fpoussin/MotoLink/GUI/res/images/explosion-hi.png

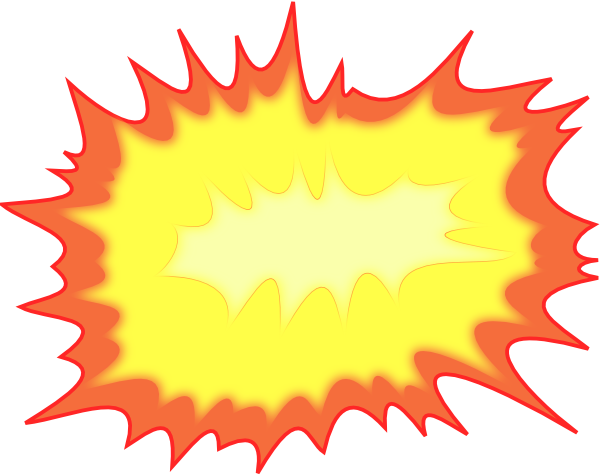
GUI/res/images/explosion-hi.png
