fpoussin/MotoLink/code/common/mcuconf_community.h

/*
    ChibiOS/RT - Copyright (C) 2014 Uladzimir Pylinsky aka barthess

    Licensed under the Apache License, Version 2.0 (the "License");
    you may not use this file except in compliance with the License.
    You may obtain a copy of the License at

        http://www.apache.org/licenses/LICENSE-2.0

    Unless required by applicable law or agreed to in writing, software
    distributed under the License is distributed on an "AS IS" BASIS,
    WITHOUT WARRANTIES OR CONDITIONS OF ANY KIND, either express or implied.
    See the License for the specific language governing permissions and
    limitations under the License.
*/

/*
 * FSMC driver system settings.
 */
#define STM32_FSMC_USE_FSMC1 FALSE
#define STM32_FSMC_FSMC1_IRQ_PRIORITY 10

/*
 * FSMC NAND driver system settings.
 */
#define STM32_NAND_USE_FSMC_NAND1 FALSE
#define STM32_NAND_USE_FSMC_NAND2 FALSE
#define STM32_NAND_USE_EXT_INT FALSE
#define STM32_NAND_DMA_STREAM STM32_DMA_STREAM_ID(2, 7)
#define STM32_NAND_DMA_PRIORITY 0
#define STM32_NAND_DMA_ERROR_HOOK(nandp) osalSysHalt("DMA failure")

/*
 * FSMC SRAM driver system settings.
 */
#define STM32_USE_FSMC_SRAM FALSE
#define STM32_SRAM_USE_FSMC_SRAM1 FALSE
#define STM32_SRAM_USE_FSMC_SRAM2 FALSE
#define STM32_SRAM_USE_FSMC_SRAM3 FLASE
#define STM32_SRAM_USE_FSMC_SRAM4 FALSE

/*
 * FSMC PC card driver system settings.
 */
#define STM32_USE_FSMC_PCARD FALSE

/*
 * FSMC SDRAM driver system settings.
 */
#define STM32_USE_FSMC_SDRAM FALSE

/*
 * EICU driver system settings.
 */
#define STM32_EICU_USE_TIM1 FALSE
#define STM32_EICU_USE_TIM2 FALSE
#define STM32_EICU_USE_TIM3 TRUE
#define STM32_EICU_USE_TIM4 FALSE
#define STM32_EICU_USE_TIM5 FALSE
#define STM32_EICU_USE_TIM8 FALSE
#define STM32_EICU_USE_TIM9 FALSE
#define STM32_EICU_USE_TIM10 FALSE
#define STM32_EICU_USE_TIM11 FALSE
#define STM32_EICU_USE_TIM12 FALSE
#define STM32_EICU_USE_TIM13 FALSE
#define STM32_EICU_USE_TIM14 FALSE
#define STM32_EICU_TIM1_IRQ_PRIORITY 7
#define STM32_EICU_TIM2_IRQ_PRIORITY 7
#define STM32_EICU_TIM3_IRQ_PRIORITY 7
#define STM32_EICU_TIM4_IRQ_PRIORITY 7
#define STM32_EICU_TIM5_IRQ_PRIORITY 7
#define STM32_EICU_TIM8_IRQ_PRIORITY 7
#define STM32_EICU_TIM9_IRQ_PRIORITY 7
#define STM32_EICU_TIM10_IRQ_PRIORITY 7
#define STM32_EICU_TIM11_IRQ_PRIORITY 7
#define STM32_EICU_TIM12_IRQ_PRIORITY 7
#define STM32_EICU_TIM13_IRQ_PRIORITY 7
#define STM32_EICU_TIM14_IRQ_PRIORITY 7

/*
 * TIMCAP driver system settings.
 */
#define STM32_TIMCAP_USE_TIM1 FALSE
#define STM32_TIMCAP_USE_TIM2 FALSE
#define STM32_TIMCAP_USE_TIM3 TRUE
#define STM32_TIMCAP_USE_TIM4 FALSE
#define STM32_TIMCAP_USE_TIM5 FALSE
#define STM32_TIMCAP_USE_TIM8 FALSE
#define STM32_TIMCAP_USE_TIM9 FALSE
#define STM32_TIMCAP_TIM1_IRQ_PRIORITY 3
#define STM32_TIMCAP_TIM2_IRQ_PRIORITY 3
#define STM32_TIMCAP_TIM3_IRQ_PRIORITY 3
#define STM32_TIMCAP_TIM4_IRQ_PRIORITY 3
#define STM32_TIMCAP_TIM5_IRQ_PRIORITY 3
#define STM32_TIMCAP_TIM8_IRQ_PRIORITY 3
#define STM32_TIMCAP_TIM9_IRQ_PRIORITY 3

/*
 * CRC driver system settings.
 */
#define STM32_CRC_USE_CRC1 TRUE
#define STM32_CRC_CRC1_DMA_IRQ_PRIORITY 5
#define STM32_CRC_CRC1_DMA_PRIORITY 2
#define STM32_CRC_CRC1_DMA_STREAM STM32_DMA_STREAM_ID(2, 1)

#define CRCSW_USE_CRC1 FALSE
#define CRCSW_CRC32_TABLE TRUE
#define CRCSW_CRC16_TABLE TRUE
#define CRCSW_PROGRAMMABLE TRUE
