fpoussin/MotoLink/code/app/tables.c

/*
 * tables.c
 *
 *  Created on: 20 nov. 2014
 *      Author: Mobyfab
 */

#include "tables.h"

/* Columns are divided by 100 */
cell_cols_t tableColumns = {0,   20,  40,  55,  70,  80,  90,  100,
                            110, 120, 130, 140, 150, 160, 165, 180};
cell_rows_t tableRows = {0, 2, 5, 7, 12, 25, 35, 50, 70, 85, 100};

cell_table_t tableAFR;
cell_table_t tableKnock;

void writeRows(uint8_t *rows, uint8_t size) {
  uint8_t i;
  for (i = 0; i < size; i++) {
    tableRows[i] = rows[i];
  }
}

void writeColumns(uint8_t *columns, uint8_t size) {
  uint8_t i;
  for (i = 0; i < size; i++) {
    tableColumns[i] = columns[i];
  }
}

CCM_FUNC bool findCell(uint8_t tp, uint16_t rpm, uint8_t *row, uint8_t *col) {
  uint8_t i, maxcol, maxrow;
  bool rowFound = false, colFound = false;

  *row = 0;
  *col = 0;
  rpm /= 100;

  maxrow = sizeof(tableRows) - 1;
  maxcol = sizeof(tableColumns) - 1;

  if (tp >= tableRows[maxrow]) {
    *row = maxrow;
    rowFound = true;
  } else if (tp <= tableRows[0]) {
    *row = 0;
    rowFound = true;
  } else {
    for (i = 0; i < maxrow; i++) {
      uint8_t h = tableRows[i];
      uint8_t h2 = tableRows[i + 1];

      if (tp >= h && tp <= h2) {
        *row = i;
        rowFound = true;
        break;
      }
    }
  }

  if (rpm >= tableColumns[maxcol]) {
    *col = maxcol;
    colFound = true;
  } else if (rpm <= tableColumns[0]) {
    *col = 0;
    colFound = true;
  } else {
    for (i = 0; i < maxcol; i++) {
      uint8_t h = tableColumns[i];
      uint8_t h2 = tableColumns[i + 1];

      if (rpm >= h && rpm <= h2) {
        *col = i;
        colFound = true;
        break;
      }
    }
  }

  return rowFound && colFound;
}
