fpoussin/MotoLink/GUI/src/mainwindow.cpp

#include "mainwindow.h"
#include <QShortcut>
#include <QSignalMapper>
#include <ui_main.h>
#include <ui_tasks.h>
#include <ui_knock.h>
#include <ui_logs.h>
#include <QFileInfo>
#include <QModelIndex>
#include <QDateTime>
#include <QItemSelection>

MainWindow::MainWindow(QWidget *parent)
    : QMainWindow(parent), mSettings("Motolink", "Motolink"), mHelpViewer(NULL), mUndoStack(NULL), mAFRModel(&mUndoStack, 7.0, 24.0, 13.0, false, false), mAFRTgtModel(&mUndoStack, 8.0, 24.0, 13.0), mKnockModel(&mUndoStack, 0, 512, 0, false, false), mFuelOffsetModel(&mUndoStack, -30, 30, 0, false, false)
{
    mMainUi = new Ui::MainWindow();
    mTasksUi = new Ui::Tasks();
    mLogsUi = new Ui::Logs();
    mSerialLogsUi = new Ui::Logs();
    mKnockGraphUi = new Ui::KnockGraph();

    mTasksWidget = new QWidget();
    mKnockGraphWidget = new QWidget;
    mLogsWidget = new QWidget();
    mSerialLogsWidget = new QWidget();

    mMainUi->setupUi(this);
    mTasksUi->setupUi(mTasksWidget);
    mKnockGraphUi->setupUi(mKnockGraphWidget);
    mLogsUi->setupUi(mLogsWidget);
    mSerialLogsUi->setupUi(mSerialLogsWidget);

    mMtl = new Motolink();
    mUpdateWizard = new UpdateWizard(mMtl);

    mUndoStack.setUndoLimit(100);

    this->setupDefaults();
    this->setupConnections();
    this->setupTabShortcuts();
    this->setupSettings();
    this->setupKnockGraph();

    mUndoView.setStack(&mUndoStack);
    mUndoView.setWindowTitle(tr("Actions History - ") + this->windowTitle());
    mHasChanged = false;

    mFastPollingTimer.setInterval(25);
    mSlowPollingTimer.setInterval(500);
    mTablesTimer.setInterval(25);
    mRedrawTimer.setInterval(25);

    this->exportToMTLFile();
    this->uiDisable();
    mHeadersUpdating = false;

    emit signalStartupComplete();

    this->log(tr("Ready"));
}

MainWindow::~MainWindow()
{
    delete mMainUi;
    delete mUpdateWizard;
    delete mTasksUi;
    delete mTasksWidget;
    delete mKnockGraphUi;
    delete mKnockGraphWidget;
    delete mLogsUi;
    delete mSerialLogsUi;
    delete mLogsWidget;
    delete mMtl;

    for (int i = 0; i < MAX_RECENT_FILES; ++i) {
        if (mRecentFilesActions[i] != NULL)
            delete mRecentFilesActions[i];
    }
}

void MainWindow::Quit()
{
    if (mHasChanged) {

        int ret = QMessageBox::question(this, tr("Confirm"),
                                        tr("Unsaved changes!\nSave file before closing?"),
                                        QMessageBox::Save | QMessageBox::Discard
                                                | QMessageBox::Cancel,
                                        QMessageBox::Cancel);

        switch (ret) {
        case QMessageBox::Save:
            this->saveFile();
            break;
        case QMessageBox::Discard:
            break;
        case QMessageBox::Cancel:
            return;
        }
    }
    qApp->quit();
}

void MainWindow::closeEvent(QCloseEvent *event)
{
    event->ignore();
    this->Quit();
}

void MainWindow::openFile(void)
{
    QString fileName(QFileDialog::getOpenFileName(this,
                                                  tr("Open Tune File"), "", tr("Tune Files (*.xml)")));

    this->openFile(fileName);
}

void MainWindow::openFile(const QString &filename)
{
    if (filename.isEmpty())
        return;

    QStringList files = mSettings.value(SETTINGS_RECENT_FILES).toStringList();

    mCurrentFile = filename;
    files.removeAll(filename);
    files.prepend(filename);
    while (files.size() > MAX_RECENT_FILES)
        files.removeLast();

    mSettings.setValue(SETTINGS_RECENT_FILES, files);
    this->updateRecentFilesActions();

    QFile file(mCurrentFile);

    if (!file.open(QFile::ReadOnly)) {
        this->log(tr("Failed to open file for reading!"));
        return;
    }

    mFile.read(&file);
    file.close();

    this->log(tr("Opened ") + filename);

    this->importFromMTLFile();
}

void MainWindow::saveFile(void)
{
    if (mCurrentFile.length() == 0) {
        this->saveFileAs();
        return;
    }

    QFile file(mCurrentFile);

    qWarning() << "Saving" << mCurrentFile;
    if (!file.open(QFile::WriteOnly)) {
        qWarning() << tr("Failed to open file for writing!") << mCurrentFile;
        this->log(tr("Failed to open file for writing!"));
        return;
    }

    file.seek(0);
    this->exportToMTLFile();
    mFile.write(&file);
    file.close();
    this->log(tr("File saved."));

    mHasChanged = false;
}

void MainWindow::saveFileAs(void)
{
    QString fileName(QFileDialog::getSaveFileName(this,
                                                  tr("Save Tune File"), "", tr("Tune Files (*.xml)")));

    if (fileName.isEmpty()) {
        return;
    }
    mCurrentFile = fileName;

    this->saveFile();
}

void MainWindow::connectMtl()
{
    if (mMtl->usbConnect()) {
        mMtl->bootAppIfNeeded();
        mMtl->readTablesHeaders();
        this->uiEnable();
        mFastPollingTimer.start();
        mSlowPollingTimer.start();
        mTablesTimer.start();
        mRedrawTimer.start();
        onReadMtlSettings();
        this->log(tr("Connected"));
    } else {
        this->log(tr("Connection Failed"));
    }
}

void MainWindow::disconnectMtl()
{
    mFastPollingTimer.stop();
    mSlowPollingTimer.stop();
    mTablesTimer.stop();
    mRedrawTimer.stop();
    mMtl->usbDisconnect();
    this->uiDisable();
    this->log(tr("Disconnected"));
}

void MainWindow::showAbout()
{
    QString Fwv = mUpdateWizard->getFwVersion();
    QMessageBox::information(this, tr("About Motolink"),
                             tr("<strong>App Version: ") + __MTL_VER__ + "</strong><br/>" + tr("<strong>Bundled firmware Version: ") + Fwv + "</strong><br/>" + tr("Built on: ") + QString(__DATE__) + " " + QString(__TIME__) + "<br/><br/>" + tr("Motolink is a smart ECU mapping interface.<br/><br/>"
                                                                                                                                                                                                                                                   "You can find more information "
                                                                                                                                                                                                                                                   "<a href=\"https://github.com/fpoussin/MotoLink\">here.</a>"));
}

void MainWindow::showUpdateDialog()
{
    mUpdateWizard->showWizard();
}

void MainWindow::setupDefaults(void)
{
    this->setWindowTitle(QString("Motolink ") + __MTL_VER__);

    mTablesModelList.append(&mAFRModel);
    mTablesModelList.append(&mAFRTgtModel);
    mTablesModelList.append(&mKnockModel);
    mTablesModelList.append(&mFuelOffsetModel);

    mTablesViewList.append(mMainUi->tableAfrMap);
    mTablesViewList.append(mMainUi->tableAfrTgt);
    mTablesViewList.append(mMainUi->tableKnk);
    mTablesViewList.append(mMainUi->tableFuelOffset);

    mAFRModel.setName(tr("AFR"));
    mAFRTgtModel.setName(tr("AFR Target"));
    mKnockModel.setName(tr("Knock"));

    mAFRModel.setId(1);
    mKnockModel.setId(2);

    mDegreeSuffix.setSuffix(QString::fromUtf8("°"));
    mPercentSuffix.setSuffix("%");

    mMainUi->tableAfrMap->setItemDelegate(&mAfrDisplay);
    mMainUi->tableAfrTgt->setItemDelegate(&mAfrDisplay);
    mMainUi->tableFuelOffset->setItemDelegate(&mPercentSuffix);

    mMainUi->tableAfrMap->setModel(&mAFRModel);
    mMainUi->tableAfrTgt->setModel(&mAFRTgtModel);
    mMainUi->tableKnk->setModel(&mKnockModel);
    mMainUi->tableFuelOffset->setModel(&mFuelOffsetModel);

    mMainUi->tableAfrMap->setMenuReadOnly(true);
    mMainUi->tableKnk->setMenuReadOnly(true);
    mMainUi->tableFuelOffset->setMenuReadOnly(true);
}

void MainWindow::setupConnections(void)
{
    QObject::connect(mMainUi->actionAbout, SIGNAL(triggered()), this, SLOT(showAbout()));
    QObject::connect(mMainUi->actionAbout_QT, SIGNAL(triggered()), qApp, SLOT(aboutQt()));
    QObject::connect(mMainUi->actionQuit, SIGNAL(triggered()), this, SLOT(Quit()));
    QObject::connect(mMainUi->actionOpen, SIGNAL(triggered()), this, SLOT(openFile()));
    QObject::connect(mMainUi->actionSave, SIGNAL(triggered()), this, SLOT(saveFile()));
    QObject::connect(mMainUi->actionSave_As, SIGNAL(triggered()), this, SLOT(saveFileAs()));
    QObject::connect(mMainUi->actionConnect, SIGNAL(triggered()), this, SLOT(connectMtl()));
    QObject::connect(mMainUi->actionDisconnect, SIGNAL(triggered()), this, SLOT(disconnectMtl()));
    QObject::connect(mMainUi->actionUpdate, SIGNAL(triggered()), this, SLOT(showUpdateDialog()));
    QObject::connect(mMainUi->actionEnglish, SIGNAL(triggered()), this, SLOT(setLanguageEnglish()));
    QObject::connect(mMainUi->actionFran_ais, SIGNAL(triggered()), this, SLOT(setLanguageFrench()));
    QObject::connect(mMainUi->actionShowHelpIndex, SIGNAL(triggered()), this, SLOT(showHelp()));
    QObject::connect(mMainUi->actionShow_tasks, SIGNAL(triggered()), this, SLOT(showTasks()));
    QObject::connect(mMainUi->actionShow_Knock_Spectrum, SIGNAL(triggered()), this, SLOT(showKnockGraph()));
    QObject::connect(mMainUi->actionShow_Logs, SIGNAL(triggered()), this, SLOT(showLogs()));
    QObject::connect(mMainUi->actionShow_Serial_Data, SIGNAL(triggered()), this, SLOT(showSerialData()));

    QObject::connect(mMainUi->actionShow_actions, SIGNAL(triggered()), &mUndoView, SLOT(show()));
    QObject::connect(mMainUi->actionUndo, SIGNAL(triggered()), &mUndoStack, SLOT(undo()));
    QObject::connect(mMainUi->actionRedo, SIGNAL(triggered()), &mUndoStack, SLOT(redo()));
    QObject::connect(&mUndoStack, SIGNAL(canRedoChanged(bool)), mMainUi->actionRedo, SLOT(setEnabled(bool)));
    QObject::connect(&mUndoStack, SIGNAL(canUndoChanged(bool)), mMainUi->actionUndo, SLOT(setEnabled(bool)));

    // Tables (color and cursor update)
    QObject::connect(&mAFRTgtModel, SIGNAL(cellValueChanged(int, int)), this, SLOT(onDataChanged()));
    QObject::connect(&mAFRTgtModel, SIGNAL(cellValueChanged(int, int)), this, SLOT(calculateFuelOffset(int, int)));
    QObject::connect(&mAFRModel, SIGNAL(cellValueChanged(int, int)), this, SLOT(calculateFuelOffset(int, int)));
    for (int i = 0; i < mTablesModelList.size(); i++) {
        TableModel *tbl = mTablesModelList.at(i);
        QObject::connect(tbl, SIGNAL(headerDataNeedSync(int, Qt::Orientation, QVariant)),
                         this, SLOT(onHeadersNeedSync(int, Qt::Orientation, QVariant)));
        //QObject::connect(tbl->view(), SIGNAL(modelUpdated(QWidget*)), mMainUi->tabMain, SLOT(setCurrentWidget(QWidget*)));
        if (tbl->id() > 1)
            QObject::connect(tbl->view(), SIGNAL(cellCleared(uint, int, int)), mMtl, SLOT(clearCell(uint, int, int)));
    }

    for (int i = 0; i < mSpinBoxList.size(); i++) {
        QSpinBox *sb = mSpinBoxList.at(i);
        QObject::connect(sb, SIGNAL(valueChanged(int)), this, SLOT(showSettingsTab()));
        QObject::connect(sb, SIGNAL(valueChanged(int)), this, SLOT(onDataChanged()));
    }

    QObject::connect(this, SIGNAL(signalStartupComplete()), &mUpdate, SLOT(getLatestVersion()));
    QObject::connect(&mUpdate, SIGNAL(newVersionAvailable(QString)), this, SLOT(showNewVersionPopup(QString)));
    QObject::connect(mUpdateWizard, SIGNAL(sendDisconnect()), this, SLOT(disconnectMtl()));

    QObject::connect(mMainUi->bTpsSet0, SIGNAL(clicked()), this, SLOT(onSetTps0Pct()));
    QObject::connect(mMainUi->bTpsSet100, SIGNAL(clicked()), this, SLOT(onSetTps100Pct()));

    QObject::connect(mMainUi->bReadMtl, SIGNAL(clicked()), this, SLOT(onReadMtlSettings()));
    QObject::connect(mMainUi->bWriteMtl, SIGNAL(clicked()), this, SLOT(onWriteMtlSettings()));

    // Recent files
    for (int i = 0; i < MAX_RECENT_FILES; ++i) {
        mRecentFilesActions[i] = new QAction(this);
        mRecentFilesActions[i]->setVisible(false);
        mRecentFilesActions[i]->setIcon(QIcon("://oxygen/32x32/actions/quickopen-file.png"));
        connect(mRecentFilesActions[i], SIGNAL(triggered()),
                this, SLOT(openRecenFile()));
        mMainUi->menuRecent_files->addAction(mRecentFilesActions[i]);
    }

    /* UI update */

    QObject::connect(&mFastPollingTimer, SIGNAL(timeout()), this, SLOT(doFastPolling()));
    QObject::connect(&mSlowPollingTimer, SIGNAL(timeout()), this, SLOT(doSlowPolling()));
    QObject::connect(&mTablesTimer, SIGNAL(timeout()), this, SLOT(doTablesPolling()));
    QObject::connect(&mRedrawTimer, SIGNAL(timeout()), this, SLOT(doSensorsRedraw()));

    QObject::connect(mMtl, SIGNAL(receivedMonitoring(TaskList const *)), this, SLOT(onMonitoringReceived(TaskList const *)));
    QObject::connect(mMtl, SIGNAL(receivedKockSpectrum(QByteArray const *)), this, SLOT(onKnockSpectrumReceived(QByteArray const *)));
    QObject::connect(mMtl, SIGNAL(receivedTables(const quint8 *, const quint8 *)), this, SLOT(onTablesReceived(const quint8 *, const quint8 *)));
    QObject::connect(mMtl, SIGNAL(receivedTablesHeaders(const quint8 *, const quint8 *)), this, SLOT(onTablesHeadersReceived(const quint8 *, const quint8 *)));
    QObject::connect(mMtl, SIGNAL(communicationError(QString)), this, SLOT(log(QString)));
    QObject::connect(mMtl, SIGNAL(communicationError(QString)), mMtl, SLOT(clearUsb()));

    QObject::connect(&mFile, SIGNAL(readFailed(QString)), this, SLOT(onSimpleError(QString)));
}

void MainWindow::setupTabShortcuts()
{
    QSignalMapper *signalMapper = new QSignalMapper(this);

    /* Assign tab shortcuts starting from F5 up to F12 */
    for (int index = 0; index < mMainUi->tabMain->count(); ++index) {
        if (index > 7)
            break;
        QShortcut *shortcut = new QShortcut(
                QKeySequence(QString("F%1").arg(index + 5)), this);

        QObject::connect(shortcut, SIGNAL(activated()),
                         signalMapper, SLOT(map()));
        signalMapper->setMapping(shortcut, index);
    }
    QObject::connect(signalMapper, SIGNAL(mapped(int)),
                     mMainUi->tabMain, SLOT(setCurrentIndex(int)));
}

void MainWindow::setupSettings()
{
    const QString lang = mSettings.value(SETTINGS_LANGUAGE, "English").toString();
    mRecentFiles = mSettings.value(SETTINGS_RECENT_FILES, QStringList()).toStringList();

    if (lang == "French") {
        this->setLanguageFrench();
    } else {
        this->setLanguageEnglish();
    }

    this->updateRecentFilesActions();
}

void MainWindow::setupKnockGraph()
{
    QCustomPlot *plot = mKnockGraphUi->mainPlot;
    mKnockFreqLabel = new QCPItemText(plot);

    plot->addGraph();
    plot->xAxis->setLabel(tr("Knock Frequency (Hertz)"));
    plot->yAxis->setLabel(tr("Knock Intensity (Volts, AC)"));
    plot->xAxis->setRange(0, FFT_FREQ);
    plot->yAxis->setRange(0, KNOCK_MAX);

    plot->addItem(mKnockFreqLabel);
    mKnockFreqLabel->setPositionAlignment(Qt::AlignTop | Qt::AlignHCenter);
    mKnockFreqLabel->position->setType(QCPItemPosition::ptAxisRectRatio);
    mKnockFreqLabel->position->setCoords(0.5, 0); // place position at center/top of axis rect
    mKnockFreqLabel->setText(tr("Loading..."));
    mKnockFreqLabel->setFont(QFont(font().family(), 16)); // make font a bit larger
    mKnockFreqLabel->setPen(QPen(Qt::black)); // show black border around text
}

void MainWindow::retranslate()
{
    mMainUi->retranslateUi(this);
    mUpdateWizard->retranslate();
    mKnockGraphUi->retranslateUi(mKnockGraphWidget);
    mTasksUi->retranslateUi(mTasksWidget);

    mMainUi->tableAfrMap->retranslate();
    mMainUi->tableAfrTgt->retranslate();
    mMainUi->tableKnk->retranslate();
    mMainUi->tableFuelOffset->retranslate();
}

void MainWindow::setLanguageEnglish()
{
    qApp->removeTranslator(&mTranslator);
    this->retranslate();
    mSettings.setValue("main/language", "English");
}

void MainWindow::setLanguageFrench()
{
    if (!mTranslator.load(":/tr/motolink_fr")) {
        qWarning() << "Failed to load translation";
        return;
    }

    qApp->installTranslator(&mTranslator);
    this->retranslate();
    mSettings.setValue("main/language", "French");
}

void MainWindow::showHelp()
{
    mHelpViewer.show();
}

void MainWindow::uiEnable()
{
    const bool toggle = true;

    mMainUi->actionConnect->setEnabled(!toggle);
    mMainUi->actionDisconnect->setEnabled(toggle);
    mMainUi->actionGet_Configuration->setEnabled(toggle);
    mMainUi->actionSend_Configuration->setEnabled(toggle);
    mMainUi->actionShow_tasks->setEnabled(toggle);
    mMainUi->actionShow_Knock_Spectrum->setEnabled(toggle);
    mMainUi->actionShow_Serial_Data->setEnabled(toggle);
    mMainUi->bReadMtl->setEnabled(toggle);
    mMainUi->bWriteMtl->setEnabled(toggle);
}

void MainWindow::uiDisable()
{
    const bool toggle = false;

    mMainUi->actionConnect->setEnabled(!toggle);
    mMainUi->actionDisconnect->setEnabled(toggle);
    mMainUi->actionGet_Configuration->setEnabled(toggle);
    mMainUi->actionSend_Configuration->setEnabled(toggle);
    mMainUi->actionShow_tasks->setEnabled(toggle);
    mMainUi->actionShow_Knock_Spectrum->setEnabled(toggle);
    mMainUi->actionShow_Serial_Data->setEnabled(toggle);
    mMainUi->bReadMtl->setEnabled(toggle);
    mMainUi->bWriteMtl->setEnabled(toggle);
}

void MainWindow::updateRecentFilesActions()
{
    QStringList files = mSettings.value(SETTINGS_RECENT_FILES).toStringList();
    const uint numRecentFiles = qMin(files.size(), (int)MAX_RECENT_FILES);

    for (uint i = 0; i < numRecentFiles; ++i) {
        QString text = QFileInfo(files[i]).fileName();
        mRecentFilesActions[i]->setText(text);
        mRecentFilesActions[i]->setData(files[i]);
        mRecentFilesActions[i]->setVisible(true);
    }
    for (int j = numRecentFiles; j < MAX_RECENT_FILES; ++j)
        mRecentFilesActions[j]->setVisible(false);
}

void MainWindow::openRecenFile()
{
    QAction *action = qobject_cast<QAction *>(sender());
    if (action)
        this->openFile(action->data().toString());
}

void MainWindow::showSettingsTab()
{
    const int index = mMainUi->tabMain->indexOf(mMainUi->tabSettings);

    if (index >= 0)
        mMainUi->tabMain->setCurrentIndex(index);
}

void MainWindow::showTasks()
{
    mTasksWidget->show();
    mTasksWidget->raise();
}

void MainWindow::showKnockGraph()
{
    mKnockGraphWidget->show();
    mKnockGraphWidget->raise();
}

void MainWindow::showSerialData()
{
    mSerialLogsWidget->show();
    mSerialLogsWidget->raise();
}

void MainWindow::showLogs()
{
    mLogsWidget->show();
    mLogsWidget->raise();
}

void MainWindow::log(const QString &msg)
{
    QString logMsg = QString("[%1] ").arg(QTime::currentTime().toString()) + msg;
    mMainUi->statusBar->showMessage(msg);
    mLogsUi->list->addItem(logMsg);
    mLogsUi->list->scrollToBottom();
}

void MainWindow::exportToMTLFile()
{
    mFile.addTable(&mAFRModel);
    mFile.addTable(&mAFRTgtModel);
    mFile.addTable(&mKnockModel);

    mFile.addProperty("RpmMult", mMainUi->dsbRpmMult->value());
    mFile.addProperty("SpeedMult", mMainUi->dsbSpeedMult->value());

    mFile.addProperty("AFRInput", mMainUi->cbAFRInput->currentIndex());

    mFile.addProperty("TPS0",
                      mMainUi->dsbTPS0->value());
    mFile.addProperty("TPS100",
                      mMainUi->dsbTPS100->value());

    mFile.addProperty("AFR0V",
                      mMainUi->dsbAFR0->value());
    mFile.addProperty("AFR5V",
                      mMainUi->dsbAFR5->value());
}

void MainWindow::importFromMTLFile()
{
    QVariant prop;

    mFile.getProperty("RpmMult", &prop);
    mMainUi->dsbRpmMult->setValue(prop.toDouble());

    mFile.getProperty("SpeedMult", &prop);
    mMainUi->dsbSpeedMult->setValue(prop.toDouble());

    mFile.getProperty("AFRInput", &prop);
    mMainUi->cbAFRInput->setCurrentIndex(prop.toInt());

    mFile.getProperty("TPS0", &prop);
    mMainUi->dsbTPS0->setValue(prop.toFloat());
    mFile.getProperty("TPS100", &prop);
    mMainUi->dsbTPS100->setValue(prop.toFloat());

    mFile.getProperty("AFR0V", &prop);
    mMainUi->dsbAFR0->setValue(prop.toFloat());
    mFile.getProperty("AFR5V", &prop);
    mMainUi->dsbAFR5->setValue(prop.toFloat());
}

void MainWindow::doFastPolling()
{
    if (mMtl->isConnected()) {
        mMtl->readSensors();
        if (mKnockGraphWidget->isVisible())
            mMtl->readKnockSpectrum();
    } else {
        mFastPollingTimer.stop();
    }
}

void MainWindow::doSlowPolling()
{
    if (mMtl->isConnected()) {
        if (mTasksWidget->isVisible())
            mMtl->readMonitoring();
    } else {
        mSlowPollingTimer.stop();
    }
}

void MainWindow::doTablesPolling()
{
    if (mMtl->isConnected()) {
        mMtl->readTables();
    } else {
        mTablesTimer.stop();
    }
}

void MainWindow::doSensorsRedraw()
{
    mMainUi->lVbat->setText(QString::number(mMtl->getVBAT()) + tr(" Volts"));

    mMainUi->lTpsVolts->setText(QString::number(mMtl->getVTPS()) + tr(" Volts"));
    mMainUi->lTpsPct->setText(QString::number(mMtl->getTPS()) + tr(" %"));

    mMainUi->lAfrVal->setText(QString::number(mMtl->getAFR()));
    mMainUi->lAfrVolts->setText(QString::number(mMtl->getVAFR()) + tr(" Volts"));
    mMainUi->lRpm->setText(QString::number(mMtl->getRPM()) + tr(" Rpm"));
    mMainUi->lRpmHertz->setText(QString::number(mMtl->getRPMHz()) + tr(" Hertz"));
    mMainUi->lSpeedHertz->setText(QString::number(mMtl->getSpeedHz()) + tr(" Hertz"));

    // Bottom progress bars
    mMainUi->pgbTps->setValue(mMtl->getTPS());

    if (mMtl->getRPM() < mMainUi->pgbRPM->maximum())
        mMainUi->pgbRPM->setValue(mMtl->getRPM());
    else
        mMainUi->pgbRPM->setValue(mMainUi->pgbRPM->maximum());
}

void MainWindow::onMonitoringReceived(const TaskList *monitoring)
{
    QTableWidgetItem *nameItem, *cpuItem;
    QTableWidget *table = mTasksUi->tableWidget;
    QString flt_str;

    table->clearContents();

    for (int i = 0; i < monitoring->size(); i++) {
        nameItem = new QTableWidgetItem();
        cpuItem = new QTableWidgetItem();

        flt_str.sprintf("%05.2f", monitoring->at(i).cpu);
        nameItem->setData(Qt::DisplayRole, monitoring->at(i).name);
        cpuItem->setData(Qt::DisplayRole, flt_str);

        if (monitoring->at(i).active) {
            nameItem->setBackgroundColor(Qt::white);
            cpuItem->setBackgroundColor(Qt::white);
        } else {
            nameItem->setBackgroundColor(Qt::lightGray);
            cpuItem->setBackgroundColor(Qt::lightGray);
        }

        if (table->rowCount() <= i)
            table->insertRow(i);
        table->setItem(i, 0, nameItem);
        table->setItem(i, 1, cpuItem);
    }

    //table->sortItems(1, Qt::DescendingOrder);
}

void MainWindow::onKnockSpectrumReceived(const QByteArray *data)
{
    QVector<double> x(SPECTRUM_SIZE), y(SPECTRUM_SIZE);
    QCustomPlot *plot = mKnockGraphUi->mainPlot;
    double max_val = 0;
    double max_freq = 0;

    for (uint i = 4; i < SPECTRUM_SIZE; i++) {
        x[i] = ((FFT_FREQ * i) / SPECTRUM_SIZE);
        y[i] = (KNOCK_MAX / 256.0) * (uchar)data->at(i);
        if (y[i] > max_val) {
            max_val = y[i];
            max_freq = x[i];
        }
    }

    mKnockFreqLabel->setText(QString::number(max_val, 'f', 2) + "V at " + QString::number(max_freq, 'f', 2) + "Hz");

    plot->graph(0)->setData(x, y);
    //plot->yAxis->setRange(0, max_val*1.2);
    plot->replot();
}

void MainWindow::onTablesReceived(const quint8 *afr, const quint8 *knock)
{
    mAFRModel.setDataFromArray(afr, 0.1f);
    mKnockModel.setDataFromArray(knock, 1.0f);
    this->setTablesCursor(mMtl->getRow(), mMtl->getColumn());
}

void MainWindow::onTablesHeadersReceived(const quint8 *columns, const quint8 *rows)
{
    mHeadersUpdating = true;
    mAFRModel.arrayToRows(rows, 11);
    mAFRModel.arrayToColumns(columns, 16);
    mHeadersUpdating = false;
}

void MainWindow::onSerialDataReceived(const QByteArray *data)
{
    QString str;
    const QString prepend(" 0x");

    for (int i = 0; i < data->size(); i++) {
        str.append(prepend + QString::number(data->at(i), 16));
    }

    mSerialLogsUi->list->addItem(str);
    mSerialLogsUi->list->scrollToBottom();
}

void MainWindow::onSetTps0Pct(void)
{
    mMainUi->dsbTPS0->setValue(mMtl->getVTPS());
}

void MainWindow::onSetTps100Pct(void)
{
    mMainUi->dsbTPS100->setValue(mMtl->getVTPS());
}

void MainWindow::onDataChanged()
{
    if (mFile.isLoading())
        return;

    mHasChanged = true;
    if (mMainUi->actionAutosave->isChecked()) {
        this->saveFile();
    }

    if (mMainUi->actionAuto_Send->isChecked()) {
    }
}

void MainWindow::onHeadersNeedSync(int section, Qt::Orientation orientation, const QVariant value)
{
    const int role = Qt::UserRole;

    for (int i = 0; i < mTablesModelList.size(); i++) {
        TableModel *tbl = mTablesModelList.at(i);
        if (tbl) {
            tbl->setHeaderData(section, orientation, value, role);
        }
    }

    quint8 rows[11];
    quint8 cols[16];
    mAFRModel.rowsToArray(rows, sizeof(rows));
    mAFRModel.columnsToArray(cols, sizeof(cols));

    if (!mHeadersUpdating)
        mMtl->writeTablesHeaders(rows, cols);
}

void MainWindow::onSimpleError(QString error)
{
    QMessageBox::critical(this, "Error", error);
}

void MainWindow::showNewVersionPopup(QString version)
{
    QMessageBox::information(this,
                             tr("New version available"),
                             tr("There is a new version available for download: ") + version
                                     + tr("<br/>You are currently using: ") + __MTL_VER__
                                     + "<br/><br/><a href='https://github.com/fpoussin/MotoLink/releases/latest'>"
                                     + tr("Download here") + "</a>");
}

void MainWindow::setTablesCursorFromSensors(uint tps, uint rpm)
{
    int row, col;
    for (int i = 0; i < mTablesModelList.size(); i++) {
        TableModel *tbl = mTablesModelList.at(i);
        if (tbl && tbl->getCell(tps, rpm, &row, &col)) {
            tbl->highlightCell(row, col);
        }
    }
}

void MainWindow::setTablesCursor(uint row, uint col)
{
    for (int i = 0; i < mTablesModelList.size(); i++) {
        TableModel *tbl = mTablesModelList.at(i);
        if (tbl) {
            tbl->highlightCell(row, col);
        }
    }
}

void MainWindow::onReadMtlSettings()
{
    if (mMtl->readSettings()) {
        // Unpack settings
        mMainUi->dsbTPS0->setValue(mMtl->getTPSMinV());
        mMainUi->dsbTPS100->setValue(mMtl->getTPSMaxV());
        mMainUi->dsbAFR0->setValue(mMtl->getAFRMinVal());
        mMainUi->dsbAFR5->setValue(mMtl->getAFRMaxVal());
        mMainUi->dsbAFROffset->setValue(mMtl->getAFROffset());
        mMainUi->dsbRpmMult->setValue(mMtl->getRpmMultiplier());
        mMainUi->dsbSpeedMult->setValue(mMtl->getSpdMultiplier());

        if (mMtl->getFunctionAFR_Disabled())
            mMainUi->cbAFRInput->setCurrentIndex(0);
        else if (mMtl->getFunctionAFR_Analog())
            mMainUi->cbAFRInput->setCurrentIndex(1);
        else if (mMtl->getFunctionAFR_MTS())
            mMainUi->cbAFRInput->setCurrentIndex(2);
        else if (mMtl->getFunctionAFR_OBD())
            mMainUi->cbAFRInput->setCurrentIndex(3);
        else if (mMtl->getFunctionAFR_Test())
            mMainUi->cbAFRInput->setCurrentIndex(4);

        if (mMtl->getFunctionInput_Direct())
            mMainUi->cbInputType->setCurrentIndex(0);
        else if (mMtl->getFunctionInput_OBD())
            mMainUi->cbInputType->setCurrentIndex(1);
        else if (mMtl->getFunctionInput_Yamaha())
            mMainUi->cbInputType->setCurrentIndex(2);
        else if (mMtl->getFunctionInput_Test())
            mMainUi->cbInputType->setCurrentIndex(3);

        if (mMtl->getSerialMode_Shell())
            mMainUi->cbSerialMode->setCurrentIndex(0);
        else if (mMtl->getSerialMode_Kline())
            mMainUi->cbSerialMode->setCurrentIndex(1);
        else if (mMtl->getSerialMode_CanBus())
            mMainUi->cbSerialMode->setCurrentIndex(2);

        mMainUi->cbRecording->setChecked(mMtl->getFunctionRecording());
        mMainUi->cbOBDEmulator->setChecked(mMtl->getFunctionOBDEmulator());

        this->log("Read settings OK");
    } else
        this->log("Read settings Fail");
}

void MainWindow::onWriteMtlSettings()
{
    mMtl->setTPSMinV(mMainUi->dsbTPS0->value());
    mMtl->setTPSMaxV(mMainUi->dsbTPS100->value());
    mMtl->setAFRMinVal(mMainUi->dsbAFR0->value());
    mMtl->setAFRMaxVal(mMainUi->dsbAFR5->value());
    mMtl->setAFROffset(mMainUi->dsbAFROffset->value());
    mMtl->setRpmMultiplier(mMainUi->dsbRpmMult->value());
    mMtl->setSpdMultiplier(mMainUi->dsbSpeedMult->value());

    switch (mMainUi->cbAFRInput->currentIndex()) {
    case 0:
        mMtl->setFunctionAFR_Disabled();
        break;

    case 1:
        mMtl->setFunctionAFR_Analog();
        break;

    case 2:
        mMtl->setFunctionAFR_MTS();
        break;

    case 3:
        mMtl->setFunctionAFR_OBD();
        break;

    case 4:
        mMtl->setFunctionAFR_Test();
        break;

    default:
        mMtl->setFunctionAFR_Disabled();
        break;
    }

    switch (mMainUi->cbInputType->currentIndex()) {
    case 0:
        mMtl->setFunctionInput_Direct();
        break;

    case 1:
        mMtl->setFunctionInput_OBD();
        break;

    case 2:
        mMtl->setFunctionInput_Yamaha();
        break;

    case 3:
        mMtl->setFunctionInput_Test();
        break;

    default:
        mMtl->setFunctionInput_Direct();
        break;
    }

    switch (mMainUi->cbSerialMode->currentIndex()) {
    case 0:
        mMtl->setSerialMode_Shell();
        break;

    case 1:
        mMtl->setSerialMode_Kline();
        break;

    case 2:
        mMtl->setSerialMode_CanBus();
        break;

    default:
        mMtl->setSerialMode_Shell();
        break;
    }

    mMtl->setFunctionRecord(mMainUi->cbRecording->isChecked());
    mMtl->setFunctionOBDEmulator(mMainUi->cbOBDEmulator->isChecked());

    if (mMtl->writeSettings()) {
        this->log("Write settings OK");
    } else
        this->log("Write settings Fail");
}

void MainWindow::calculateFuelOffset(int row, int column)
{
    float target, value, offset;
    QStandardItem *itm;
    QModelIndex idx;

    itm = mAFRTgtModel.item(row, column);
    if (!itm->data(Qt::EditRole).isValid())
        return;
    target = (float)itm->data(Qt::EditRole).toFloat() / 10.0;

    itm = mAFRModel.item(row, column);
    if (!itm->data(Qt::EditRole).isValid())
        return;
    value = itm->data(Qt::EditRole).toFloat() / 10.0;

    offset = (value - target) / ((value + target) / 2.0) * 100.0;

    idx = mFuelOffsetModel.index(row, column);
    mFuelOffsetModel.setData(idx, offset, Qt::UserRole);
}
